Creative-Difficulty/mSCKee/journal-imgs/fixing-before.png

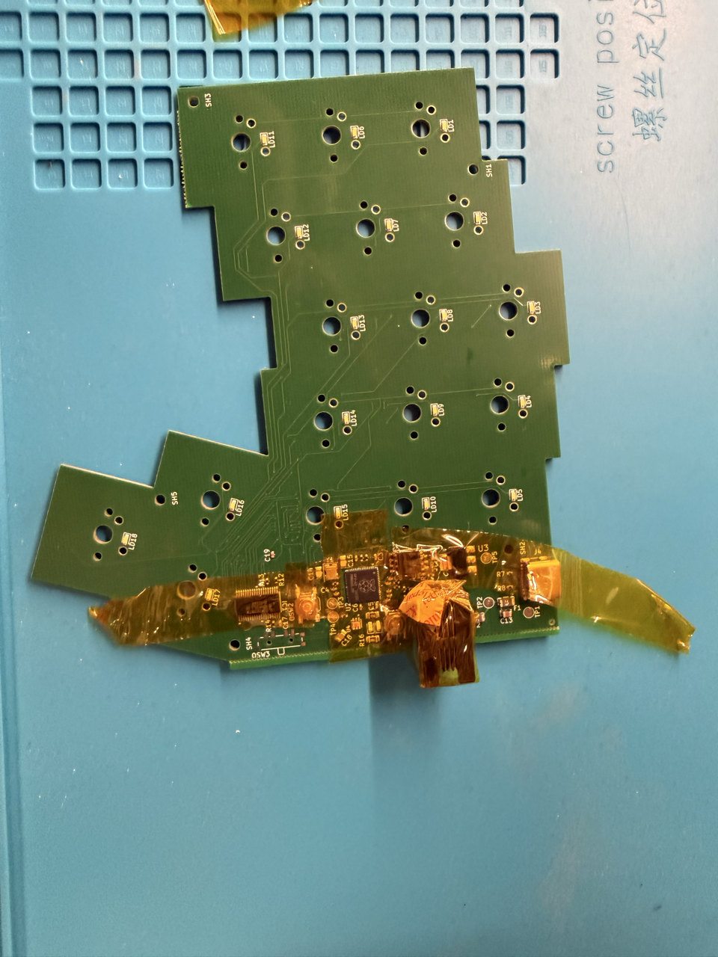
journal-imgs/fixing-before.png
